casouri/cq-80/docs/img/sanding-sponge.jpeg

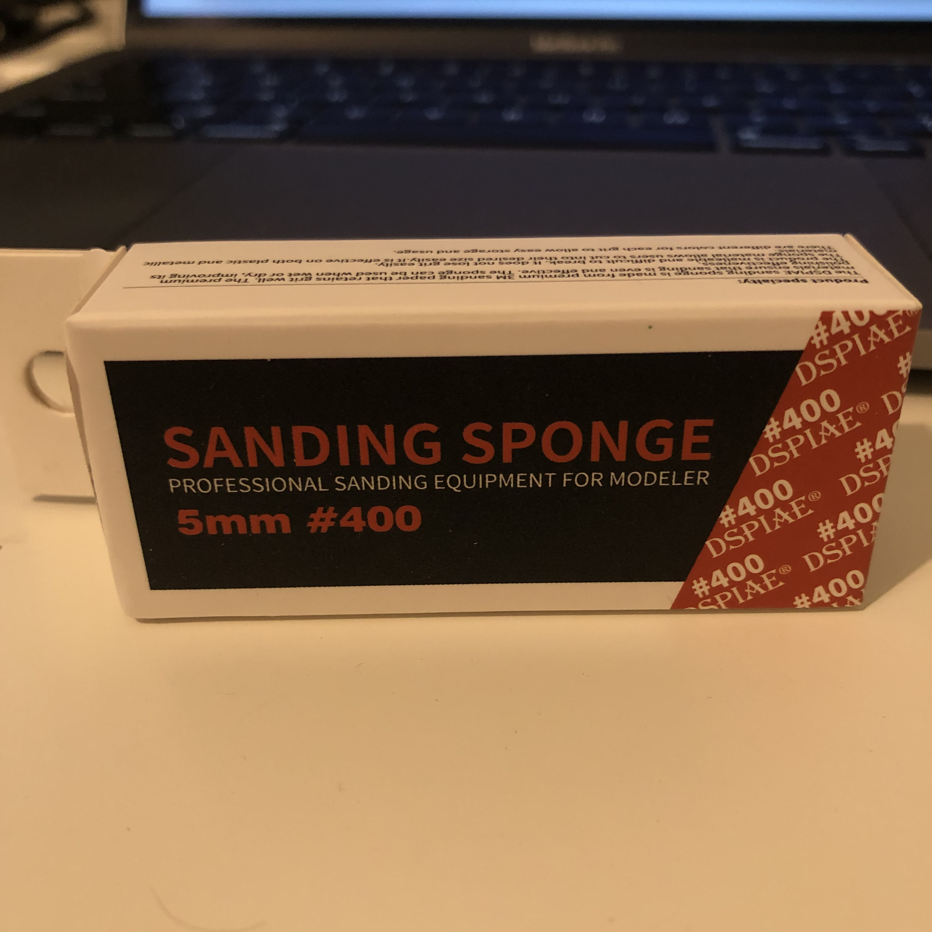
docs/img/sanding-sponge.jpeg
